sdp8483/base_convert/back_pannel_pcb/images/back_panel_pcb.png

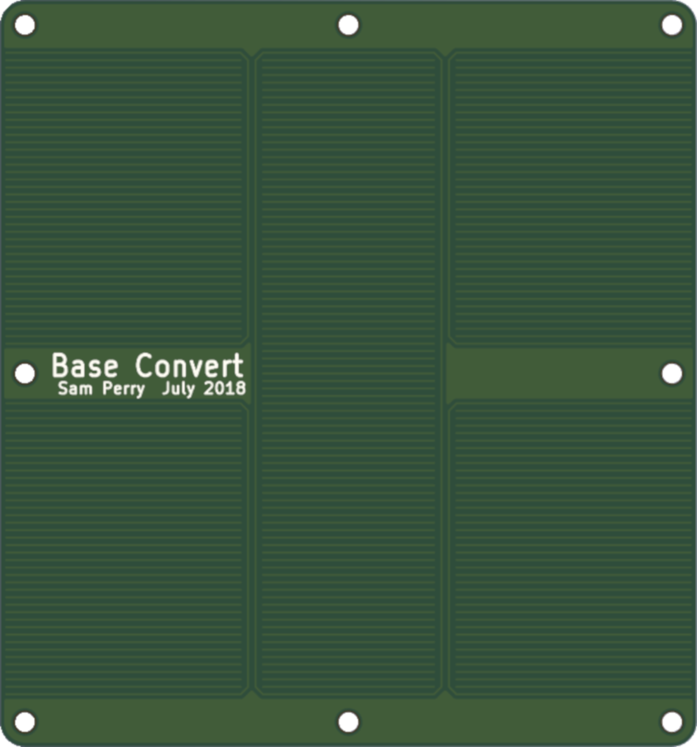
back_pannel_pcb/images/back_panel_pcb.png
