sdp8483/base_convert/images/base_convert_render.png

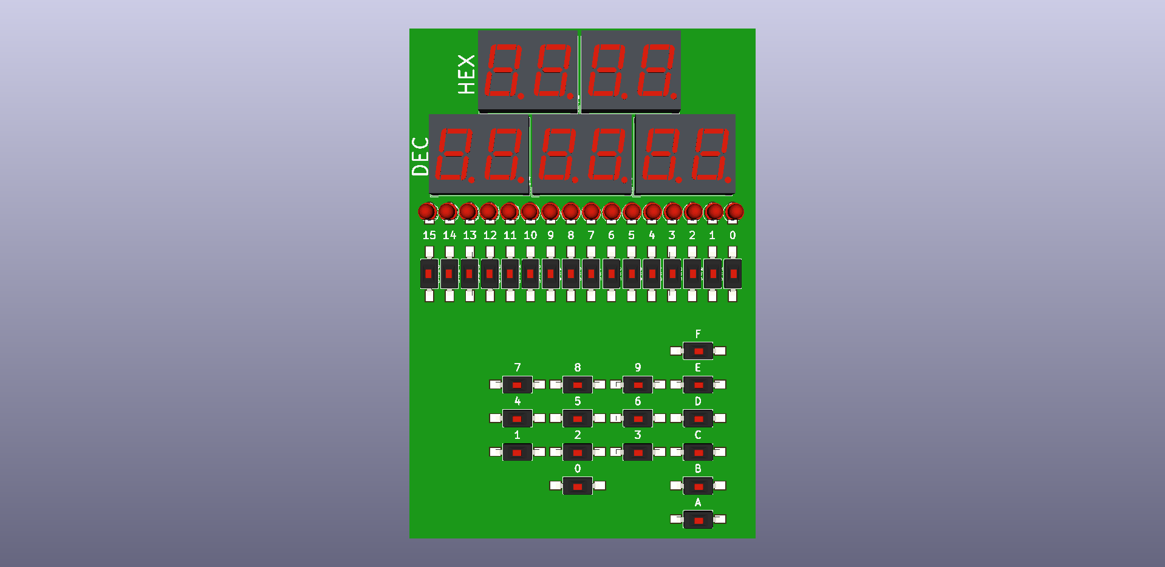
images/base_convert_render.png
