sdp8483/base_convert/images/label/sn_label.png

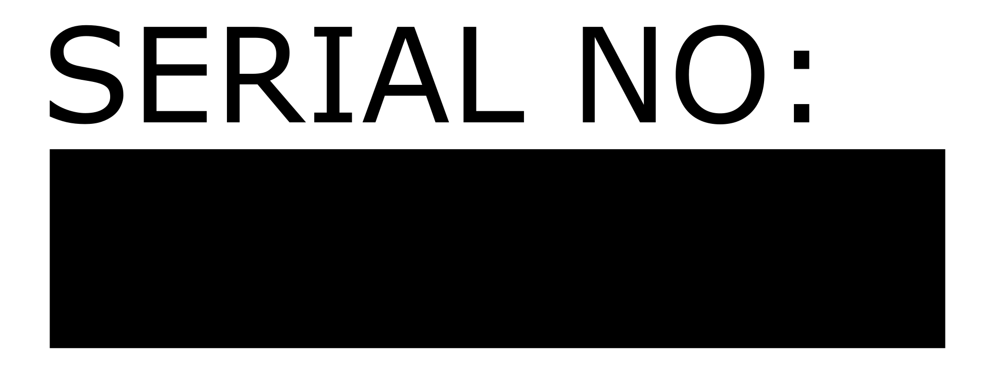
images/label/sn_label.png
