sdp8483/base_convert/images/Rev A/03_BaseConvert_Back.png

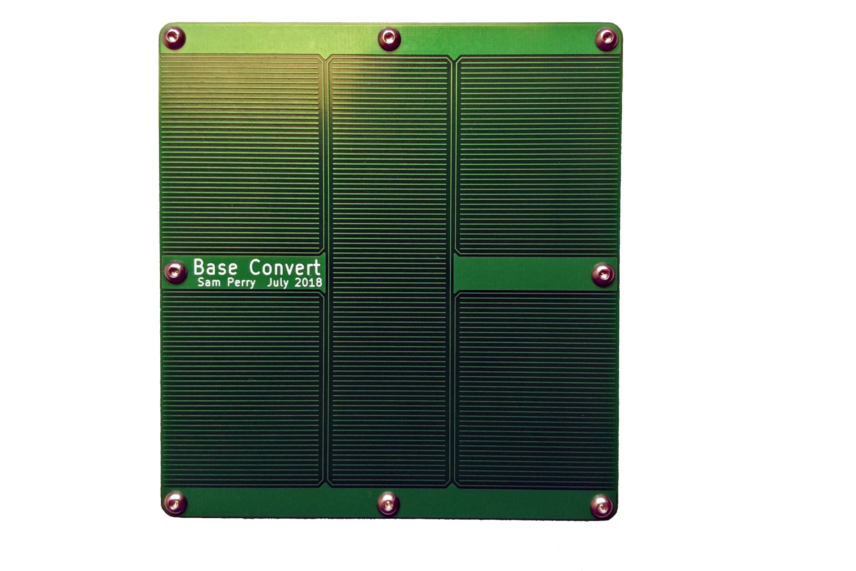
images/Rev A/03_BaseConvert_Back.png
