sdp8483/base_convert/images/Rev A/Raw JPEG/2018-09-03 08.54.56.jpg

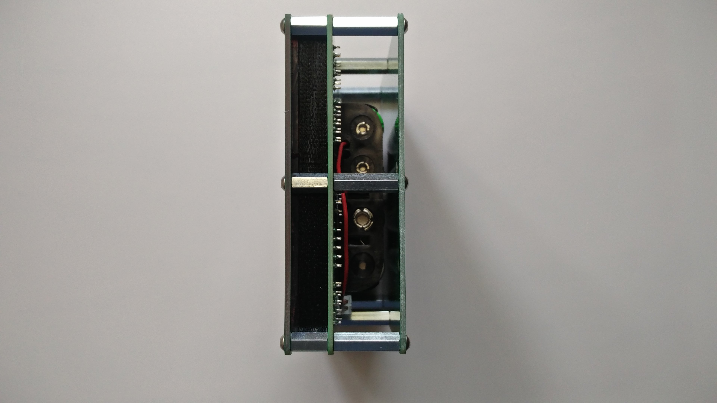
images/Rev A/Raw JPEG/2018-09-03 08.54.56.jpg
