sdp8483/base_convert/images/Rev A/Raw JPEG/2018-09-03 09.13.10.jpg

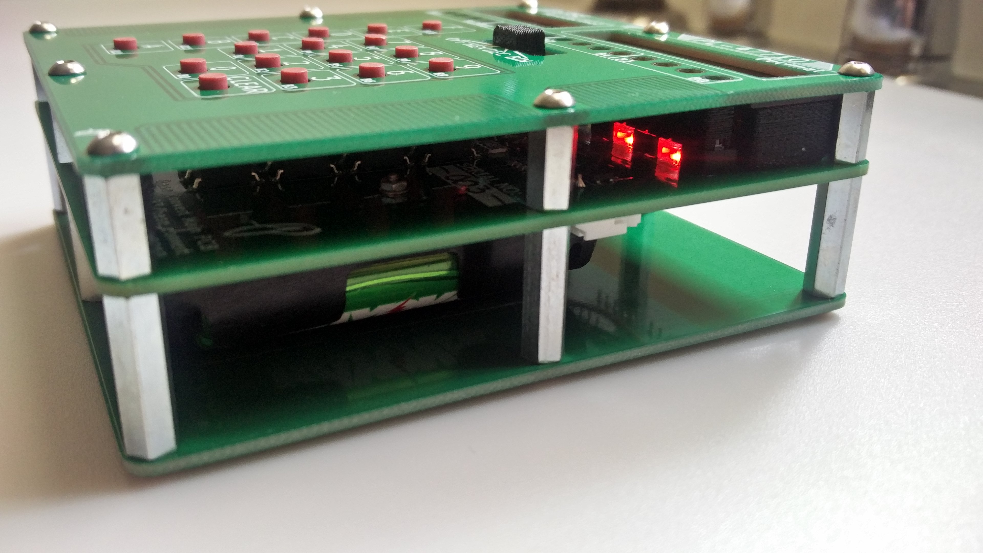
images/Rev A/Raw JPEG/2018-09-03 09.13.10.jpg
