sdp8483/base_convert/main_pcb/pcb_renders/images/base_convert_front_dim.png

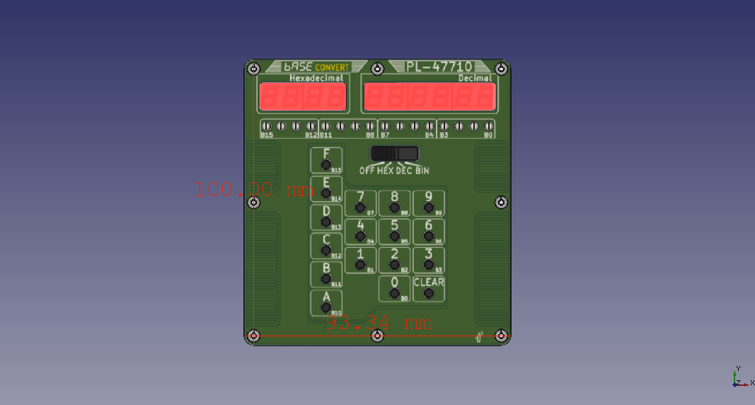
main_pcb/pcb_renders/images/base_convert_front_dim.png
