sdp8483/base_convert/main_pcb/pcb_renders/images/base_convert_assembly_bottom.png

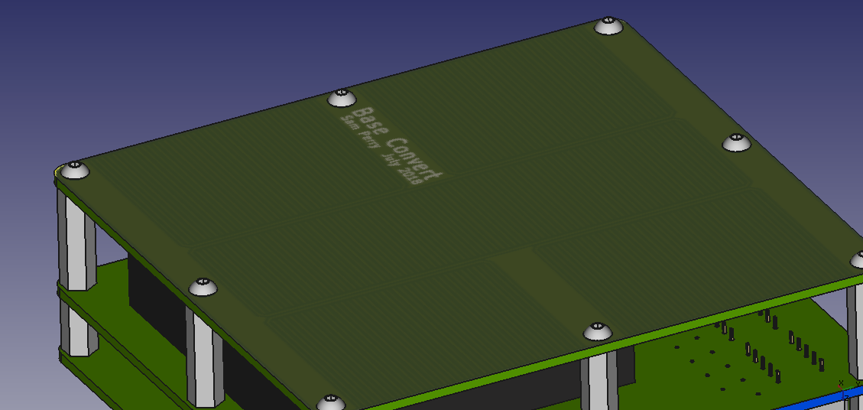
main_pcb/pcb_renders/images/base_convert_assembly_bottom.png
