sdp8483/base_convert/firmware/base_convert/button.h

/*
 * button.h
 *
 *  Created on: Jun 1, 2018
 *      Author: Sam
 */

#ifndef BUTTON_H_
#define BUTTON_H_

#define REVA                                    // REV A remove separate BIN keypad

#define WAITFORRELESE(pin, colPin)  while(!(pin & colPin)){ WDT_waitForRelease();}

// Mode slide switch inputs
#define MODEDIR     P2DIR
#define MODEIN      P2IN
#define MODEOUT     P2OUT
#define MODEREN     P2REN
#define DECPIN      BIT6
#define HEXPIN      BIT5
#define BINPIN      BIT7

#define DECMODE     0                           // decimal input mode
#define HEXMODE     1                           // hex input mode
#define BINMODE     2                           // binary input mode
#define NOMODE      3                           // something is wrong!

// clear button
#define CLEARIN     P8IN
#define CLEAROUT    P8OUT
#define CLEARDIR    P8DIR
#define CLEARREN    P8REN
#define CLEARPIN    BIT0

// keypad rows and columns
#define KPOUT   P1OUT                           // keypad port
#define KPIN    P1IN
#define KPDIR   P1DIR                           // keypad dir
#define KPREN   P1REN
#define KPROW0  BIT7
#define KPROW1  BIT6
#define KPROW2  BIT5
#define KPROW3  BIT4
#define KPCOL0  BIT3
#define KPCOL1  BIT2
#define KPCOL2  BIT1
#define KPCOL3  BIT0

// bin keypad rows and columns
#ifdef REVA
#define BKPOUT  P1OUT
#define BKPIN   P1IN
#define BKPDIR  P1DIR
#define BKPREN  P1REN
#define BKPROW0 BIT7
#define BKPROW1 BIT6
#define BKPROW2 BIT5
#define BKPROW3 BIT4
#define BKPCOL0 BIT3
#define BKPCOL1 BIT2
#define BKPCOL2 BIT1
#define BKPCOL3 BIT0
#else
#define BKPOUT  P5OUT
#define BKPIN   P5IN
#define BKPDIR  P5DIR
#define BKPREN  P5REN
#define BKPROW0 BIT7
#define BKPROW1 BIT6
#define BKPROW2 BIT5
#define BKPROW3 BIT4
#define BKPCOL0 BIT3
#define BKPCOL1 BIT2
#define BKPCOL2 BIT1
#define BKPCOL3 BIT0
#endif

void modeSetup(void);                           // setup input pins for mode slide switch
void clearSetup(void);                          // setup input pin for clear button
void keySetup(void);                            // setup DEC/HEX keypad
static void WDT_startDebounce(void);            // from TI Low_Power_Keypad example
static void WDT_waitForRelease(void);           // wait for button to be released delay
uint8_t modeGet(void);                          // get current position of slide switch
uint16_t clearPoll(uint16_t num);               // check if clear button was pressed
uint16_t keyPollHEX(uint16_t num);              // check keypad input, update num if necessary, Hex input mode
uint16_t keyPollDEC(uint16_t num);              // check keypad input, update num if necessary, Decimal input mode
uint16_t keyPollBIN(uint16_t num);              // check keypad input, update num if necessary, binary input mode

#endif /* BUTTON_H_ */
