sdp8483/base_convert/firmware/base_convert/func.h

/*
 * func.h
 *
 *  Created on: Jun 6, 2018
 *      Author: Sam
 */

#ifndef FUNC_H_
#define FUNC_H_

uint16_t decSafeShift(uint32_t num, uint8_t input); // safely shift in decimal input to prevent integer overflow

#endif /* FUNC_H_ */
